tergav17/Z80-MegaMapper/CPLD/Nabu/registers.v

`timescale 1ns / 1ps
//////////////////////////////////////////////////////////////////////////////////
// Company: 
// Engineer: Gavin Tersteeg 
// 
// Create Date:    01:21:04 05/16/2024 
// Design Name: 
// Module Name:    registers 
// Project Name: 
// Target Devices: 
// Tool versions: 
// Description: Handles picking up and putting stuff onto the data bus 
//
// Dependencies: 
//
// Revision: 
// Revision 0.01 - File Created
// Additional Comments: 
//
//////////////////////////////////////////////////////////////////////////////////
module registers(
    inout [7:0] data,
    input wr_n,
    input rd_n,
    input m1_n,
    input record_isr_en,
    input read_isr_en,
    input write_ctrl_en,
    input reset_n,
    input io_violation_occured,
    output [3:0] ctrl_out
    );

// Define control and instruction registers
reg[3:0] ctrl_reg;
reg[6:0] isr_reg;

// Logic for reading the control register
assign ctrl_out = ctrl_reg;

// Logic for controlling the contents of the control register
always @(posedge wr_n or negedge reset_n)
begin
   if (!reset_n)
      ctrl_reg <= 4'b0000;
   else if (write_ctrl_en)
      ctrl_reg <= data[3:0];
end

// Logic for reading the output register
assign data = (!rd_n && read_isr_en) ? {io_violation_occured, isr_reg[6:2], isr_reg[1:0]} : 8'bZZZZZZZZ;

// Logic for controlling the contents of the instruction registers
always @(posedge m1_n)
begin
   if (record_isr_en)
      isr_reg <= {data[7:3], data[1:0]};
end

endmodule
